mirrorganger/GalernaDsp/olas/ola-1.png

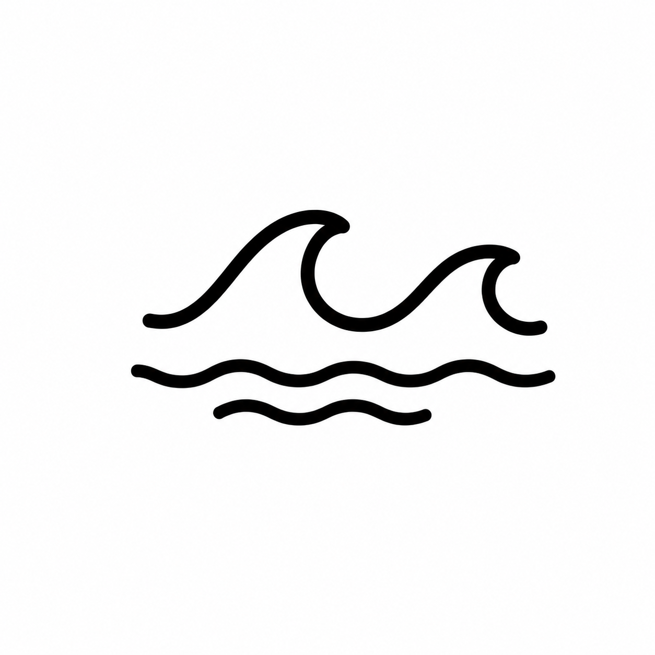
olas/ola-1.png
